Prasanth-acc/RELAY-PIPE-GUIDED-ROVER-FOR-MONITORING-LANDSLIDE-AFFECTED-COAL-MINES/CAD Models/IMG_20250614_151522.jpg

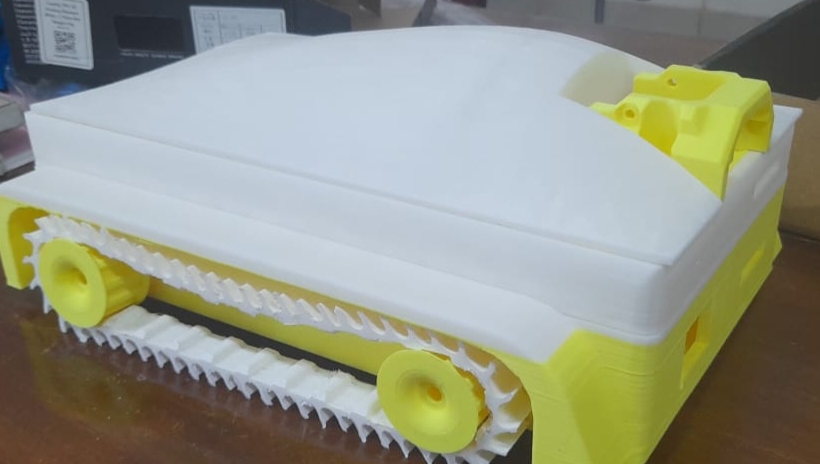
CAD Models/IMG_20250614_151522.jpg
